swanmatch/keeb_rubykaigi2023/bottom-outline/images/82246354.png

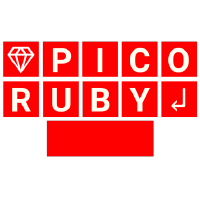
bottom-outline/images/82246354.png
