swanmatch/keeb_rubykaigi2023/images/03.jpg

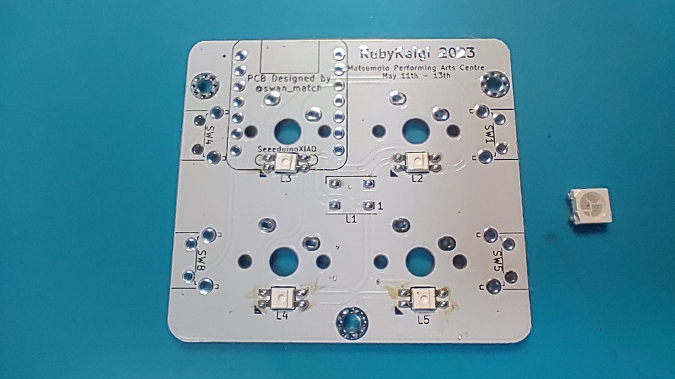
images/03.jpg
