swanmatch/keeb_rubykaigi2023/bottom-outline/pcb.kicad_sch

## KiCad design bottom-outline/pcb.kicad_sch (2023-02-09)

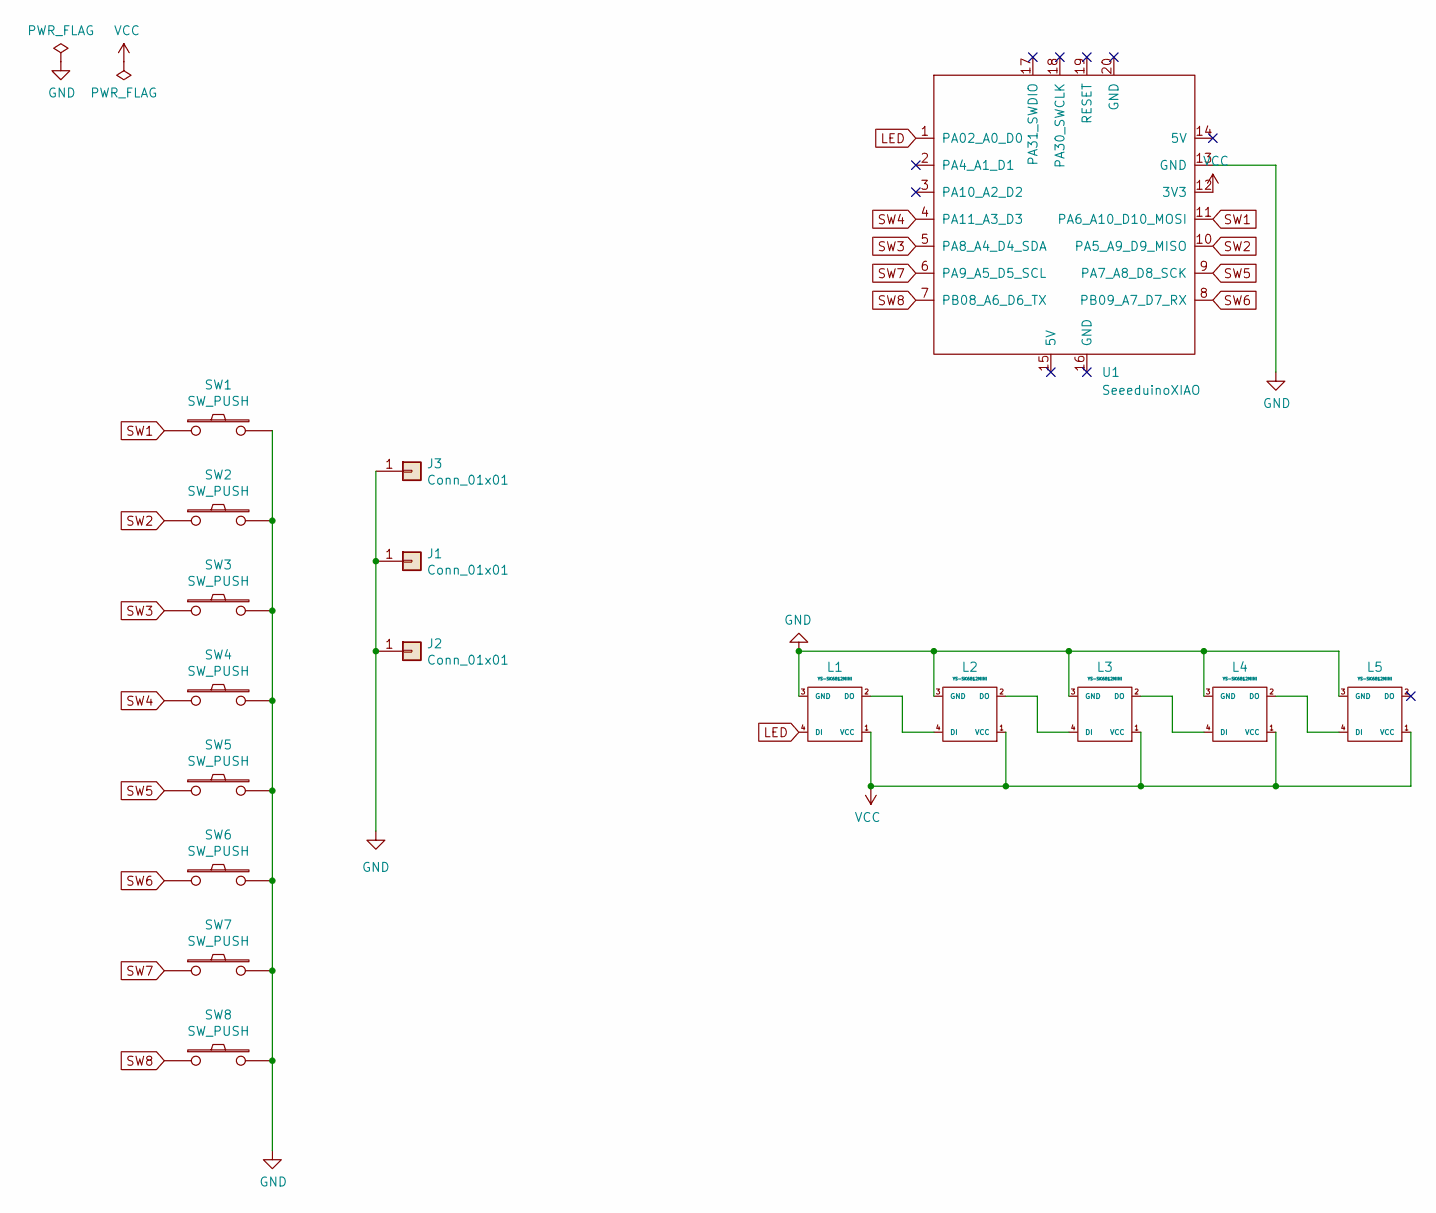
[picture p25: schematic pcb.kicad_sch]

Parts:
J1, J2, J3: Conn_01x01; MountingHole_2.2mm_M2_Pad_Via
L1: YS-SK6812MINI; LED_WS2812B_PLCC4_5.0x5.0mm_P3.2mm
L2, L3, L4, L5: YS-SK6812MINI; YS-SK6812MINI-E
SW1, SW4, SW5, SW8: SW_PUSH; SW_Tactile_SPST_Angled_PTS645Vx39-2LFS
SW2, SW3, SW6, SW7: SW_PUSH; MX_1U
U1: SeeeduinoXIAO; Seeeduino XIAO TH only

Connections:
GND: J1.1, J2.1, J3.1, L1.3 (GND), L2.3 (GND), L3.3 (GND), L4.3 (GND), L5.3 (GND), SW1.2, SW2.2, SW3.2, SW4.2, SW5.2, SW6.2, SW7.2, SW8.2, U1.13 (GND)
LED: L1.4 (DI), U1.1 (PA02_A0_D0)
unnamed: L1.2 (DO), L2.4 (DI)
unnamed: L2.2 (DO), L3.4 (DI)
unnamed: L3.2 (DO), L4.4 (DI)
unnamed: L4.2 (DO), L5.4 (DI)
SW1: SW1.1, U1.11 (PA6_A10_D10_MOSI)
SW2: SW2.1, U1.10 (PA5_A9_D9_MISO)
SW3: SW3.1, U1.5 (PA8_A4_D4_SDA)
SW4: SW4.1, U1.4 (PA11_A3_D3)
SW5: SW5.1, U1.9 (PA7_A8_D8_SCK)
SW6: SW6.1, U1.8 (PB09_A7_D7_RX)
SW7: SW7.1, U1.6 (PA9_A5_D5_SCL)
SW8: SW8.1, U1.7 (PB08_A6_D6_TX)
VCC: L1.1 (VCC), L2.1 (VCC), L3.1 (VCC), L4.1 (VCC), L5.1 (VCC), U1.12 (3V3)
